dchwebb/Retrospector/Retrospector_v3/Src/initialisation.cpp

#include "stm32h743xx.h"
#include "initialisation.h"
#include "DigitalDelay.h"
#include "sdram.h"

// Clock overview:
// Main clock 4MHz: 8MHz (HSE) / 2 (M) * 200 (N) / 2 (P) = 400MHz
// SDRAM: 200MHz: Defaulted to D1 domain AHB prescaler (RCC_D1CFGR_HPRE_3) ie main clock /2 = 200MHz (AKA HCLK3)
// I2S: Peripheral Clock (AKA per_ck) set to HSI = 64MHz
// ADC: Peripheral Clock (AKA per_ck) set to HSI = 64MHz

// 8MHz (HSE) / 2 (M) * 200 (N) / 2 (P) = 400MHz
#define PLL_M1 2
#define PLL_N1 200
#define PLL_P1 1			// 0000001: pll1_p_ck = vco1_ck / 2
#define PLL_Q1 4			// This is used for I2S clock: 8MHz (HSE) / 2 (M) * 200 (N) / 4 (Q) = 200MHz
#define PLL_R1 2

void InitClocks()
{
	RCC->APB4ENR |= RCC_APB4ENR_SYSCFGEN;			// Enable System configuration controller clock

	// Voltage scaling - see Datasheet page 113. VOS1 > 300MHz; VOS2 > 200MHz; VOS3 < 200MHz
	PWR->CR3 &= ~PWR_CR3_SCUEN;						// Supply configuration update enable - this must be deactivated or VOS ready does not come on
	PWR->D3CR |= PWR_D3CR_VOS;						// Configure voltage scaling level 1 before engaging overdrive (0b11 = VOS1)
	while ((PWR->CSR1 & PWR_CSR1_ACTVOSRDY) == 0);	// Check Voltage ready 1= Ready, voltage level at or above VOS selected level

	RCC->CR |= RCC_CR_HSEON;						// Turn on external oscillator
	while ((RCC->CR & RCC_CR_HSERDY) == 0);			// Wait till HSE is ready

	// Clock source to High speed external and main (M) dividers
	RCC->PLLCKSELR = RCC_PLLCKSELR_PLLSRC_HSE |
	                 PLL_M1 << RCC_PLLCKSELR_DIVM1_Pos;

	// PLL 1 dividers
	RCC->PLL1DIVR = (PLL_N1 - 1) << RCC_PLL1DIVR_N1_Pos |
			        PLL_P1 << RCC_PLL1DIVR_P1_Pos |
			        (PLL_Q1 - 1) << RCC_PLL1DIVR_Q1_Pos |
			        (PLL_R1 - 1) << RCC_PLL1DIVR_R1_Pos;

	RCC->PLLCFGR |= RCC_PLLCFGR_PLL1RGE_2;			// 10: The PLL1 input (ref1_ck) clock range frequency is between 4 and 8 MHz (Will be 4MHz for 8MHz clock divided by 2)
	RCC->PLLCFGR &= ~RCC_PLLCFGR_PLL1VCOSEL;		// 0: Wide VCO range:192 to 836 MHz (default after reset)	1: Medium VCO range:150 to 420 MHz
	RCC->PLLCFGR |= RCC_PLLCFGR_DIVP1EN | RCC_PLLCFGR_DIVQ1EN;		// Enable divider outputs

	RCC->CR |= RCC_CR_PLL1ON;						// Turn on main PLL
	while ((RCC->CR & RCC_CR_PLL1RDY) == 0);		// Wait till PLL is ready

	// Peripheral scalers
	RCC->D1CFGR |= RCC_D1CFGR_HPRE_3;				// D1 domain AHB prescaler - divide 400MHz by 2 for 200MHz - this is then divided for all APB clocks below
	RCC->D1CFGR |= RCC_D1CFGR_D1PPRE_2; 			// Clock divider for APB3 clocks - set to 4 for 100MHz: 100: hclk / 2
	RCC->D2CFGR |= RCC_D2CFGR_D2PPRE1_2;			// Clock divider for APB1 clocks - set to 4 for 100MHz: 100: hclk / 2
	RCC->D2CFGR |= RCC_D2CFGR_D2PPRE2_2;			// Clock divider for APB2 clocks - set to 4 for 100MHz: 100: hclk / 2
	RCC->D3CFGR |= RCC_D3CFGR_D3PPRE_2;				// Clock divider for APB4 clocks - set to 4 for 100MHz: 100: hclk / 2

	RCC->CFGR |= RCC_CFGR_SW_PLL1;					// System clock switch: 011: PLL1 selected as system clock
	while ((RCC->CFGR & RCC_CFGR_SWS_Msk) != (RCC_CFGR_SW_PLL1 << RCC_CFGR_SWS_Pos));		// Wait until PLL has been selected as system clock source

	// By default Flash latency is set to 7 wait states - set to 4 for now but may need to increase
	FLASH->ACR = (FLASH->ACR & ~FLASH_ACR_LATENCY) | FLASH_ACR_LATENCY_5WS;
	while ((FLASH->ACR & FLASH_ACR_LATENCY_Msk) != FLASH_ACR_LATENCY_5WS);

	SystemCoreClockUpdate();						// Update SystemCoreClock (system clock frequency) derived from settings of oscillators, prescalers and PLL
}

GpioPin debugPinA			{GPIOB, 7, GpioPin::Type::Output};			// PB7
GpioPin debugPinB			{GPIOB, 8, GpioPin::Type::Output};			// PB8

void InitHardware()
{
	InitClocks();									// Configure the clock and PLL
	InitSysTick();

	InitADC();
	InitDAC();										// DAC used to output Wet/Dry mix levels
#ifndef NOEXTRAM
	InitSDRAM_16160();								// Initialise 32MB SDRAM
#endif
	InitCache();									// Configure MPU to not cache memory regions where DMA buffers reside
	InitLEDSPI();									// Initialise SPI/DAM for LED controller

	RCC->AHB4ENR |= RCC_AHB4ENR_GPIOBEN;			// GPIO port B clock

	// MODER: 00: Input, 01: General purpose output mode, 10: Alternate function mode, 11: Analog mode (reset state)
	// PUPDR: 00: No pull-up, pull-down, 01: Pull-up, 10: Pull-down

	// PB7 (D), PB8 (C) - I2C/debug
	GPIOB->MODER &= ~GPIO_MODER_MODE7_1;			// PB7: debug pin
	GPIOB->MODER &= ~GPIO_MODER_MODE8_1;			// PB8: debug pin

}

void InitCache()
{
	// Use the Memory Protection Unit (MPU) to set up a region of memory with data caching disabled for use with DMA buffers
	MPU->RNR = 0;									// Memory region number
	MPU->RBAR = reinterpret_cast<uint32_t>(&ADC_array);	// Store the address of the ADC_array into the region base address register

	MPU->RASR = (0b11  << MPU_RASR_AP_Pos)   |		// All access permitted
				(0b001 << MPU_RASR_TEX_Pos)  |		// Type Extension field: See truth table on p228 of Cortex M7 programming manual
				(1     << MPU_RASR_S_Pos)    |		// Shareable: provides data synchronization between bus masters. Eg a processor with a DMA controller
				(0     << MPU_RASR_C_Pos)    |		// Cacheable
				(0     << MPU_RASR_B_Pos)    |		// Bufferable (ignored for non-cacheable configuration)
				(17    << MPU_RASR_SIZE_Pos) |		// 256KB - D2 is actually 288K (size is log 2(mem size) - 1 ie 2^18 = 256k)
				(1     << MPU_RASR_ENABLE_Pos);		// Enable MPU region


	MPU->RNR = 1;									// Memory region number
	MPU->RBAR = reinterpret_cast<uint32_t>(&led); 	// Store the address of the led DMA buffer into the region base address register

	MPU->RASR = (0b11  << MPU_RASR_AP_Pos)   |		// All access permitted
				(0b001 << MPU_RASR_TEX_Pos)  |		// Type Extension field: See truth table on p228 of Cortex M7 programming manual
				(1     << MPU_RASR_S_Pos)    |		// Shareable: provides data synchronization between bus masters. Eg a processor with a DMA controller
				(0     << MPU_RASR_C_Pos)    |		// Cacheable
				(0     << MPU_RASR_B_Pos)    |		// Bufferable (ignored for non-cacheable configuration)
				(15    << MPU_RASR_SIZE_Pos) |		// 64KB - D3 (size is log 2(mem size) - 1 ie 2^16 = 64k)
				(1     << MPU_RASR_ENABLE_Pos);		// Enable MPU region



	MPU->CTRL |= (1 << MPU_CTRL_PRIVDEFENA_Pos) |	// Enable PRIVDEFENA - this allows use of default memory map for memory areas other than those specific regions defined above
				 (1 << MPU_CTRL_ENABLE_Pos);		// Enable the MPU

	// Enable data and instruction caches
	SCB_EnableDCache();
	SCB_EnableICache();
}


void InitSysTick()
{
	SysTick_Config(SystemCoreClock / SYSTICK);		// gives 1ms
	NVIC_SetPriority(SysTick_IRQn, 0);
}


void InitDAC()
{
	// DAC1_OUT2 on PA5
	RCC->AHB4ENR |= RCC_AHB4ENR_GPIOAEN;			// GPIO port clock
	RCC->APB1LENR |= RCC_APB1LENR_DAC12EN;			// Enable DAC Clock

	DAC1->CR |= DAC_CR_EN1;							// Enable DAC using PA4 (DAC_OUT1)
	DAC1->MCR &= DAC_MCR_MODE1_Msk;					// Mode = 0 means Buffer activated, Connected to external pin

	DAC1->CR |= DAC_CR_EN2;							// Enable DAC using PA5 (DAC_OUT2)
	DAC1->MCR &= DAC_MCR_MODE2_Msk;					// Mode = 0 means Buffer activated, Connected to external pin
}


void InitAdcPins(ADC_TypeDef* ADC_No, std::initializer_list<uint8_t> channels) {
	uint8_t sequence = 1;

	for (auto channel: channels) {
		// NB reset mode of GPIO pins is 0b11 = analog mode so shouldn't need to change
		ADC_No->PCSEL |= 1 << channel;					// ADC channel preselection register

		// Set conversion sequence to order ADC channels are passed to this function
		if (sequence < 5) {
			ADC_No->SQR1 |= channel << (sequence * 6);
		} else if (sequence < 10) {
			ADC_No->SQR2 |= channel << ((sequence - 5) * 6);
		} else if (sequence < 15)  {
			ADC_No->SQR3 |= channel << ((sequence - 10) * 6);
		} else {
			ADC_No->SQR4 |= channel << ((sequence - 15) * 6);
		}

		// 000: 1.5 ADC clock cycles; 001: 2.5 cycles; 010: 8.5 cycles;	011: 16.5 cycles; 100: 32.5 cycles; 101: 64.5 cycles; 110: 387.5 cycles; 111: 810.5 cycles
		if (channel < 10)
			ADC_No->SMPR1 |= 0b010 << (3 * channel);
		else
			ADC_No->SMPR2 |= 0b010 << (3 * (channel - 10));

		sequence++;
	}
}

// Settings used for both ADC1 and ADC2
void InitADC()
{
	// Configure clocks
	RCC->AHB4ENR |= RCC_AHB4ENR_GPIOAEN;			// GPIO port clock
	RCC->AHB4ENR |= RCC_AHB4ENR_GPIOBEN;
	RCC->AHB4ENR |= RCC_AHB4ENR_GPIOCEN;

	RCC->AHB1ENR |= RCC_AHB1ENR_ADC12EN;

	// 00: pll2_p_ck default, 01: pll3_r_ck clock, 10: per_ck clock*
	RCC->D3CCIPR |= RCC_D3CCIPR_ADCSEL_1;			// ADC clock selection: 10: per_ck clock (hse_ck, hsi_ker_ck or csi_ker_ck according to CKPERSEL in RCC->D1CCIPR p.353)
	RCC->AHB1ENR |= RCC_AHB1ENR_DMA1EN;

	ADC12_COMMON->CCR |= ADC_CCR_PRESC_0;			// Set prescaler to ADC clock divided by 2 (if 64MHz = 32MHz)

	InitADC1();
	InitADC2();
}


/*-----------------------------------------------------------------------------------------------------------------
ADC Channels are distributed across ADC1 and ADC2 for faster conversions. Audio channels on ADC1 for better quality.
Both insert data into ADC_array at different offsets.
 ADC1:
	0	PA3 ADC12_INP15		AUDIO_IN_L
	1	PA2 ADC12_INP14		AUDIO_IN_R
	2	PA1 ADC1_INP17		DELAY_POT_R
	3	PA0 ADC1_INP16		DELAY_CV_SCALED_R
ADC2:
	0	PC5 ADC12_INP8		WET_DRY_MIX
	1	PB1 ADC12_INP5		DELAY_POT_L
	2	PA6 ADC12_INP3 		DELAY_CV_SCALED_L
	3	PB0 ADC12_INP9		FEEDBACK_POT
	4	PA7 ADC12_INP7		FEEDBACK_CV_SCALED
	5	PC4 ADC12_INP4		FILTER_CV_SCALED
	6	PC1 ADC123_INP11 	FILTER_POT
*/

void InitADC1()
{
	// Initialize ADC peripheral
	DMA1_Stream1->CR &= ~DMA_SxCR_EN;
//	DMA1_Stream1->CR |= DMA_SxCR_CIRC;				// Circular mode to keep refilling buffer
	DMA1_Stream1->CR |= DMA_SxCR_MINC;				// Memory in increment mode
	DMA1_Stream1->CR |= DMA_SxCR_PSIZE_0;			// Peripheral size: 8 bit; 01 = 16 bit; 10 = 32 bit
	DMA1_Stream1->CR |= DMA_SxCR_MSIZE_0;			// Memory size: 8 bit; 01 = 16 bit; 10 = 32 bit
	DMA1_Stream1->CR |= DMA_SxCR_PL_0;				// Priority: 00 = low; 01 = Medium; 10 = High; 11 = Very High

	DMA1_Stream1->FCR &= ~DMA_SxFCR_FTH;			// Disable FIFO Threshold selection
	DMA1->LIFCR = 0x3F << DMA_LIFCR_CFEIF1_Pos;		// clear all five interrupts for this stream

	DMAMUX1_Channel1->CCR |= 9; 					// DMA request MUX input 9 = adc1_dma (See p.695)
	DMAMUX1_ChannelStatus->CFR |= DMAMUX_CFR_CSOF1; // Channel 1 Clear synchronization overrun event flag

	ADC1->CR &= ~ADC_CR_DEEPPWD;					// Deep powDMA1_Stream2own: 0: ADC not in deep-power down	1: ADC in deep-power-down (default reset state)
	ADC1->CR |= ADC_CR_ADVREGEN;					// Enable ADC internal voltage regulator

	// Wait until voltage regulator settled
	volatile uint32_t wait_loop_index = (SystemCoreClock / (100000UL * 2UL));
	while (wait_loop_index != 0UL) {
		wait_loop_index--;
	}
	while ((ADC1->CR & ADC_CR_ADVREGEN) != ADC_CR_ADVREGEN) {}

	ADC1->CFGR |= ADC_CFGR_CONT;					// 1: Continuous conversion mode for regular conversions
	ADC1->CFGR |= ADC_CFGR_OVRMOD;					// Overrun Mode 1: ADC_DR register is overwritten with the last conversion result when an overrun is detected.
	ADC1->CFGR |= ADC_CFGR_DMNGT_0;					// Data Management configuration 01: DMA One Shot Mode selected, 11: DMA Circular Mode selected

	// Boost mode 1: Boost mode on. Must be used when ADC clock > 20 MHz.
	ADC1->CR |= ADC_CR_BOOST_1;						// Note this sets reserved bit according to SFR - HAL has notes about silicon revision

	// For scan mode: set number of channels to be converted
	ADC1->SQR1 |= (ADC1_BUFFER_LENGTH - 1);

	// Start calibration
	ADC1->CR |= ADC_CR_ADCALLIN;					// Activate linearity calibration (as well as offset calibration)
	ADC1->CR |= ADC_CR_ADCAL;
	while ((ADC1->CR & ADC_CR_ADCAL) == ADC_CR_ADCAL) {};


	/*--------------------------------------------------------------------------------------------
	Configure ADC Channels to be converted:
	0	PA3 ADC12_INP15		AUDIO_IN_L
	1	PA2 ADC12_INP14		AUDIO_IN_R
	2	PA1 ADC1_INP17		DELAY_POT_R
	3	PA0 ADC1_INP16		DELAY_CV_SCALED_R
	*/
	InitAdcPins(ADC1, {15, 14, 17, 16});


	// Enable ADC
	ADC1->CR |= ADC_CR_ADEN;
	while ((ADC1->ISR & ADC_ISR_ADRDY) == 0) {}

	DMAMUX1_ChannelStatus->CFR |= DMAMUX_CFR_CSOF1; // Channel 1 Clear synchronization overrun event flag
	DMA1->LIFCR = 0x3F << DMA_LIFCR_CFEIF1_Pos;		// clear all five interrupts for this stream

	DMA1_Stream1->NDTR |= ADC1_BUFFER_LENGTH;		// Number of data items to transfer (ie size of ADC buffer)
	DMA1_Stream1->PAR = (uint32_t)(&(ADC1->DR));	// Configure the peripheral data register address 0x40022040
	DMA1_Stream1->M0AR = (uint32_t)(ADC_array);		// Configure the memory address (note that M1AR is used for double-buffer mode) 0x24000040

	DMA1_Stream1->CR |= DMA_SxCR_EN;				// Enable DMA and wait
	wait_loop_index = (SystemCoreClock / (100000UL * 2UL));
	while (wait_loop_index != 0UL) {
	  wait_loop_index--;
	}

	ADC1->CR |= ADC_CR_ADSTART;						// Start ADC
}



void TriggerADC1()
{
	ADC1->CR |= ADC_CR_ADSTART;
	DMA1->LIFCR |= DMA_LIFCR_CTCIF1 | DMA_LIFCR_CHTIF1;
	DMA1_Stream1->CR |= DMA_SxCR_EN;
}


void InitADC2()
{
	// Initialize ADC peripheral
	DMA1_Stream2->CR &= ~DMA_SxCR_EN;
	DMA1_Stream2->CR |= DMA_SxCR_CIRC;				// Circular mode to keep refilling buffer
	DMA1_Stream2->CR |= DMA_SxCR_MINC;				// Memory in increment mode
	DMA1_Stream2->CR |= DMA_SxCR_PSIZE_0;			// Peripheral size: 8 bit; 01 = 16 bit; 10 = 32 bit
	DMA1_Stream2->CR |= DMA_SxCR_MSIZE_0;			// Memory size: 8 bit; 01 = 16 bit; 10 = 32 bit
	DMA1_Stream2->CR |= DMA_SxCR_PL_0;				// Priority: 00 = low; 01 = Medium; 10 = High; 11 = Very High

	DMA1_Stream2->FCR &= ~DMA_SxFCR_FTH;			// Disable FIFO Threshold selection
	DMA1->LIFCR = 0x3F << DMA_LIFCR_CFEIF2_Pos;		// clear all five interrupts for this stream

	DMAMUX1_Channel2->CCR |= 10; 					// DMA request MUX input 10 = adc2_dma (See p.695)
	DMAMUX1_ChannelStatus->CFR |= DMAMUX_CFR_CSOF2; // Channel 2 Clear synchronization overrun event flag

	ADC2->CR &= ~ADC_CR_DEEPPWD;					// Deep power down: 0: ADC not in deep-power down	1: ADC in deep-power-down (default reset state)
	ADC2->CR |= ADC_CR_ADVREGEN;					// Enable ADC internal voltage regulator

	// Wait until voltage regulator settled
	volatile uint32_t wait_loop_index = (SystemCoreClock / (100000UL * 2UL));
	while (wait_loop_index != 0UL) {
		wait_loop_index--;
	}
	while ((ADC2->CR & ADC_CR_ADVREGEN) != ADC_CR_ADVREGEN) {}

	ADC2->CFGR |= ADC_CFGR_CONT;					// 1: Continuous conversion mode for regular conversions
	ADC2->CFGR |= ADC_CFGR_OVRMOD;					// Overrun Mode 1: ADC_DR register is overwritten with the last conversion result when an overrun is detected.
	ADC2->CFGR |= ADC_CFGR_DMNGT;					// Data Management configuration 11: DMA Circular Mode selected

	// Boost mode 1: Boost mode on. Must be used when ADC clock > 20 MHz.
	ADC2->CR |= ADC_CR_BOOST_1;						// Note this sets reserved bit according to SFR - HAL has notes about silicon revision
	ADC2->SQR1 |= (ADC2_BUFFER_LENGTH - 1);			// For scan mode: set number of channels to be converted

	// Start calibration
	ADC2->CR |= ADC_CR_ADCALLIN;					// Activate linearity calibration (as well as offset calibration)
	ADC2->CR |= ADC_CR_ADCAL;
	while ((ADC2->CR & ADC_CR_ADCAL) == ADC_CR_ADCAL) {};

	/* Configure ADC Channels to be converted:
	0	PC5 ADC12_INP8		WET_DRY_MIX
	1	PB1 ADC12_INP5		DELAY_POT_L
	2	PA6 ADC12_INP3 		DELAY_CV_SCALED_L
	3	PB0 ADC12_INP9		FEEDBACK_POT
	4	PA7 ADC12_INP7		FEEDBACK_CV_SCALED
	5	PC4 ADC12_INP4		FILTER_CV_SCALED
	6	PC1 ADC123_INP11 	FILTER_POT
	*/
	InitAdcPins(ADC2, {8, 5, 3, 9, 7, 4, 11});

	// Enable ADC
	ADC2->CR |= ADC_CR_ADEN;
	while ((ADC2->ISR & ADC_ISR_ADRDY) == 0) {}

	DMAMUX1_ChannelStatus->CFR |= DMAMUX_CFR_CSOF2; // Channel 2 Clear synchronization overrun event flag
	DMA1->LIFCR = 0x3F << DMA_LIFCR_CFEIF2_Pos;		// clear all five interrupts for this stream

	DMA1_Stream2->NDTR |= ADC2_BUFFER_LENGTH;		// Number of data items to transfer (ie size of ADC buffer)
	DMA1_Stream2->PAR = reinterpret_cast<uint32_t>(&(ADC2->DR));	// Configure the peripheral data register address 0x40022040
	DMA1_Stream2->M0AR = reinterpret_cast<uint32_t>(&ADC_array[ADC1_BUFFER_LENGTH]);		// Configure the memory address (note that M1AR is used for double-buffer mode) 0x24000040

	DMA1_Stream2->CR |= DMA_SxCR_EN;				// Enable DMA and wait
	wait_loop_index = (SystemCoreClock / (100000UL * 2UL));
	while (wait_loop_index != 0UL) {
		wait_loop_index--;
	}

	ADC2->CR |= ADC_CR_ADSTART;						// Start ADC
}



void InitI2S()
{
	RCC->APB1LENR |= RCC_APB1LENR_SPI2EN;			// Enable SPI clock

	GpioPin::Init(GPIOB, 9, GpioPin::Type::AlternateFunction, 5, GpioPin::DriveStrength::High);		//  PB9 I2S2_WS AF5
	GpioPin::Init(GPIOD, 3, GpioPin::Type::AlternateFunction, 5, GpioPin::DriveStrength::High);		//  PD3 I2S2_CK  AF5
	GpioPin::Init(GPIOC, 3, GpioPin::Type::AlternateFunction, 5, GpioPin::DriveStrength::High);		//  PC3 I2S2_SDO AF5

	// Configure SPI (Shown as SPI2->CGFR in SFR)
	SPI2->I2SCFGR |= SPI_I2SCFGR_I2SMOD;			// I2S Mode
	SPI2->I2SCFGR |= SPI_I2SCFGR_I2SCFG_1;			// I2S configuration mode: 00=Slave transmit; 01=Slave receive; 10=Master transmit*; 11=Master receive

	// Use a 16 bit data length but pack into the upper 16 bits of a 32 bit word
	//SPI2->I2SCFGR &= ~SPI_I2SCFGR_DATLEN;			// Data Length 00=16-bit; 01=24-bit; 10=32-bit
	SPI2->I2SCFGR |= SPI_I2SCFGR_DATLEN_1;			// Data Length 00=16-bit; 01=24-bit; *10=32-bit
	SPI2->I2SCFGR |= SPI_I2SCFGR_CHLEN;				// Channel Length = 32bits

	SPI2->CFG1 |= SPI_CFG1_UDRCFG_1;				// In the event of underrun resend last transmitted data frame
	SPI2->CFG1 |= 0x1f << SPI_CFG1_DSIZE_Pos;		// Data size to 32 bits (FIFO holds 16 bytes = 4 x 32 bit words)
	SPI2->CFG1 |= 1 << SPI_CFG1_FTHLV_Pos;			// FIFO threshold level. 0001: 2-data; 0010: 3 data; 0011: 4 data

	/* I2S Clock
		FS = I2SxCLK / [(32*2)*((2*I2SDIV)+ODD))]
		PER_CLK = 64MHz	(HSI)			64000000  / (32*2  * ((2 * 10) + 1)) = 47619.05
	*/
	RCC->D2CCIP1R |= RCC_D2CCIP1R_SPI123SEL_2;		// 000: pll1_q_ck (default); 001: pll2_p_ck; 010: pll3_p_ck; 011: I2S_CKIN; 100: per_ck
	SPI2->I2SCFGR |= (10 << SPI_I2SCFGR_I2SDIV_Pos);// Set I2SDIV to 45 with Odd factor prescaler
	SPI2->I2SCFGR |= SPI_I2SCFGR_ODD;

	SPI2->CR1 |= SPI_CR1_SPE;						// Enable I2S

	SPI2->TXDR = (int32_t)0;						// Preload the FIFO
	SPI2->TXDR = (int32_t)0;
	SPI2->TXDR = (int32_t)0;
	SPI2->TXDR = (int32_t)0;

	//SPI2->IER |= SPI_IER_TXPIE;						// Enable interrupt when TxFIFO threshold reached
	SPI2->IER |= (SPI_IER_TXPIE | SPI_IER_UDRIE);	// Enable interrupt when FIFO has free slot or underrun occurs
	NVIC_SetPriority(SPI2_IRQn, 2);					// Lower is higher priority
	NVIC_EnableIRQ(SPI2_IRQn);


	SPI2->CR1 |= SPI_CR1_CSTART;					// Start I2S
}


void suspendI2S()
{
	SPI2->CR1 |= SPI_CR1_CSUSP;
	while ((SPI2->SR & SPI_SR_SUSP) == 0);
}

void resumeI2S()
{
	extern DigitalDelay delay;
	delay.LR = left;

	// to allow resume from debugging ensure suspended then clear buffer underrun flag
	SPI2->CR1 |= SPI_CR1_CSUSP;
	while ((SPI2->SR & SPI_SR_SUSP) == 0);
	SPI2->IFCR |= SPI_IFCR_UDRC;

	// Clear suspend state and resume
	SPI2->IFCR |= SPI_IFCR_SUSPC;
	while ((SPI2->SR & SPI_SR_SUSP) != 0);
	SPI2->CR1 |= SPI_CR1_CSTART;
}

void InitDebugTimer()
{
	// Configure timer to use in internal debug timing
	RCC->APB1LENR |= RCC_APB1LENR_TIM3EN;
	TIM3->ARR = 65535;
	TIM3->PSC = 1;
	TIM3->CR1 |= TIM_CR1_CEN;
}



void InitLEDSPI()
{
	// Initialises SPI and DMA for controlling 3 RGB LEDs with Toshiba TB62781 9-way LED control (with 3k3 ohm resistors draws aroung 17mA from 5V)

	// By default clock is from APB2 peripheral clock at 100MHz (RCC_D2CFGR_D2PPRE2)
	RCC->APB4ENR |= RCC_APB4ENR_SPI6EN;

	GpioPin::Init(GPIOG, 13, GpioPin::Type::AlternateFunction, 5);		//  PG13 (128) SPI6_SCK AF5
	GpioPin::Init(GPIOG, 14, GpioPin::Type::AlternateFunction, 5);		//  PG14 (219) SPI6_MOSI  AF5

	SPI6->CR1 |= SPI_CR1_SSI;						// Internal slave select
	SPI6->CFG1 |= SPI_CFG1_MBR_2 | SPI_CFG1_MBR_0;	// Master Baud rate p2238: 100: SPI clock/32; 101: SPI clock/64
	SPI6->CFG2 |= SPI_CFG2_COMM_0;					// 00: full-duplex, *01: simplex transmitter, 10: simplex receiver, 11: half-duplex
	SPI6->CFG2 |= SPI_CFG2_SSM;						// Software slave management (ie do not use external pin)
	SPI6->CFG2 |= SPI_CFG2_SSOM;					// SS output management in master mode
	SPI6->CFG2 |= SPI_CFG2_MASTER;					// Master mode

	// Configure DMA
	RCC->AHB4ENR |= RCC_AHB4ENR_BDMAEN;

	BDMA_Channel0->CCR &= ~BDMA_CCR_MSIZE;			// Memory size: 8 bit; 01 = 16 bit; 10 = 32 bit
	BDMA_Channel0->CCR &= ~BDMA_CCR_PSIZE;			// Peripheral size: 8 bit; 01 = 16 bit; 10 = 32 bit
	BDMA_Channel0->CCR |= BDMA_CCR_DIR;				// data transfer direction: 00: peripheral-to-memory; 01: memory-to-peripheral; 10: memory-to-memory
	BDMA_Channel0->CCR |= BDMA_CCR_PL_0;			// Priority: 00 = low; 01 = Medium; 10 = High; 11 = Very High
	BDMA_Channel0->CCR |= BDMA_CCR_MINC;			// Memory in increment mode

	BDMA_Channel0->CPAR = (uint32_t)(&(SPI6->TXDR));// Configure the peripheral data register address

	DMAMUX2_Channel0->CCR |= 12; 					// DMA request MUX input 12 = spi6_tx_dma (See p.697)
	DMAMUX2_ChannelStatus->CFR |= DMAMUX_CFR_CSOF0; // Channel 5 Clear synchronization overrun event flag
}


void InitBootloaderTimer()
{
	// Timer clock operates at SysClk / 2  [specifically  ((hclk / HPRE) / D2PPRE1) * 2] = 200MHz
	RCC->APB1LENR |= RCC_APB1LENR_TIM2EN;
	TIM2->PSC = 0;									// [prescaler is PSC + 1] 200MHz / 1 = 200MHz
	TIM2->ARR = 2083;								// Set auto reload register 200MHz / 2083 = 96kHz

	TIM2->DIER |= TIM_DIER_UIE;						// DMA/interrupt enable register
	NVIC_SetPriority(TIM2_IRQn, 1);					// Lower is higher priority
	NVIC_EnableIRQ(TIM2_IRQn);

	TIM2->CR1 |= TIM_CR1_CEN;
	TIM2->EGR |= TIM_EGR_UG;						//  Re-initializes counter and generates update of registers
}


void DisableBootloaderTimer()
{
	TIM2->CR1 &= ~TIM_CR1_CEN;
	TIM2->DIER &= ~TIM_DIER_UIE;					// DMA/interrupt enable register
}


#ifdef UNUSED
// Unused
void Init_WS2812_SPI()
{
	// Initialises SPI with DMA to send data to string of WS2812B smart RGB LEDs. This uses a hacky SPI format to send serial data in NRZ format.
	// Note this requires 3x bit padding + extra dummy bytes to workaround MOSI line idling high (draws around 40mA at 5V)
	// SPI Pins:
	// PF7 (19) SPI5_SCK (only required for debugging)
	// PF9 (21) SPI5_MOSI

	// By default clock is from APB2 peripheral clock at 100MHz (RCC_D2CFGR_D2PPRE2)
	RCC->APB2ENR |= RCC_APB2ENR_SPI5EN;
	RCC->AHB4ENR |= RCC_AHB4ENR_GPIOFEN;			// GPIO port clock

	// PF7 (19) SPI5_SCK
	GPIOF->MODER  &= ~GPIO_MODER_MODE7_0;			// 10: Alternate function mode
	GPIOF->AFR[0] |= 5 << GPIO_AFRL_AFSEL7_Pos;		// Alternate Function 5 (SPI5)

	// PF9 (21) SPI5_MOSI
	GPIOF->MODER  &= ~GPIO_MODER_MODE9_0;			// 10: Alternate function mode
	GPIOF->AFR[1] |= 5 << GPIO_AFRH_AFSEL9_Pos;		// Alternate Function 5 (SPI5)

	// Configure SPI
	SPI5->CR1 |= SPI_CR1_SSI;						// Internal slave select
	SPI5->CFG1 |= SPI_CFG1_MBR_2;					// Master Baud rate p2238:  100: SPI master clock/32
	SPI5->CFG2 |= SPI_CFG2_COMM_0;					// 00: full-duplex, *01: simplex transmitter, 10: simplex receiver, 11: half-duplex
	SPI5->CFG2 |= SPI_CFG2_SSM;						// Software slave management (ie do not use external pin)
	SPI5->CFG2 |= SPI_CFG2_SSOM;					// SS output management in master mode
	SPI5->CFG2 |= SPI_CFG2_MASTER;					// Master mode
	SPI5->CFG2 |= SPI_CFG2_CPHA;					// Clock phase - this setting potentially reduces risk of MOSI line idling high (See p9 of dm00725181)

	// Configure DMA
	RCC->AHB1ENR |= RCC_AHB1ENR_DMA1EN;

	DMA1_Stream5->CR &= ~DMA_SxCR_MSIZE;			// Memory size: 8 bit; 01 = 16 bit; 10 = 32 bit
	DMA1_Stream5->CR &= ~DMA_SxCR_PSIZE;			// Peripheral size: 8 bit; 01 = 16 bit; 10 = 32 bit
	DMA1_Stream5->CR |= DMA_SxCR_DIR_0;				// data transfer direction: 00: peripheral-to-memory; 01: memory-to-peripheral; 10: memory-to-memory
	DMA1_Stream5->CR |= DMA_SxCR_PL_0;				// Priority: 00 = low; 01 = Medium; 10 = High; 11 = Very High
	DMA1_Stream5->CR |= DMA_SxCR_MINC;				// Memory in increment mode
	DMA1_Stream5->FCR &= ~DMA_SxFCR_FTH;			// FIFO threshold selection

	DMA1_Stream5->PAR = (uint32_t)(&(SPI5->TXDR));	// Configure the peripheral data register address

	DMAMUX1_Channel5->CCR |= 86; 					// DMA request MUX input 86 = spi5_tx_dma (See p.695) NB If using SPI6 need DMAMux2
	DMAMUX1_ChannelStatus->CFR |= DMAMUX_CFR_CSOF5; // Channel 5 Clear synchronization overrun event flag
}

// Unused
void InitI2C()
{
	//	Enable GPIO and I2C clocks
	RCC->APB1LENR |= RCC_APB1LENR_I2C1EN;			// I2C1 Peripheral Clocks Enable
	RCC->D2CCIP2R &= ~RCC_D2CCIP2R_I2C123SEL;		// Clock selection: 00: rcc_pclk1 (default); 01: pll3_r_ck; 10: hsi_ker_ck; 11: csi_ker_ck
	RCC->AHB4ENR |= RCC_AHB4ENR_GPIOBEN;			// GPIO port clock

	RCC->AHB1ENR |= RCC_AHB1ENR_DMA1EN;

	// Initialize I2C DMA peripheral
	DMA1_Stream0->CR &= ~DMA_SxCR_EN;
	DMA1_Stream0->CR &= ~DMA_SxCR_CIRC;				// Disable Circular mode to keep refilling buffer
	DMA1_Stream0->CR |= DMA_SxCR_MINC;				// Memory in increment mode
	DMA1_Stream0->CR &= ~DMA_SxCR_PSIZE_0;			// Peripheral size: 00 = 8 bit; 01 = 16 bit; 10 = 32 bit
	DMA1_Stream0->CR &= ~DMA_SxCR_MSIZE_0;			// Memory size: 00 = 8 bit; 01 = 16 bit; 10 = 32 bit
	DMA1_Stream0->CR |= DMA_SxCR_PL_0;				// Priority: 00 = low; 01 = Medium; 10 = High; 11 = Very High
	DMA1_Stream0->CR |= DMA_SxCR_DIR_0;				// data transfer direction: 00: peripheral-to-memory; 01: memory-to-peripheral; 10: memory-to-memory				// Priority: 00 = low; 01 = Medium; 10 = High; 11 = Very High

	DMA1_Stream0->FCR &= ~DMA_SxFCR_FTH;			// Disable FIFO Threshold selection
	DMA1->LIFCR = 0x3F << DMA_LIFCR_CFEIF0_Pos;		// clear all five interrupts for this stream

	DMAMUX1_Channel0->CCR |= 34; 					// DMA request MUX input 34 = i2c1_tx_dma (See p.695)
	DMAMUX1_ChannelStatus->CFR |= DMAMUX_CFR_CSOF0; // Channel 0 Clear synchronization overrun event flag


	// PB7: I2C1_SDA [alternate function AF4]
	GPIOB->OTYPER |= GPIO_OTYPER_OT7;				// Set pin output to Open Drain
	GPIOB->MODER &= ~GPIO_MODER_MODE7_0;			// 10: Alternate function mode
	GPIOB->AFR[0] |= 4 << GPIO_AFRL_AFSEL7_Pos;		// Alternate Function 4 (I2C1)

	// PB8: I2C1_SCL [alternate function AF4]
	GPIOB->OTYPER |= GPIO_OTYPER_OT8;				// Set pin output to Open Drain
	GPIOB->MODER &= ~GPIO_MODER_MODE8_0;			// 10: Alternate function mode
	GPIOB->AFR[1] |= 4 << GPIO_AFRH_AFSEL8_Pos;		// Alternate Function 4 (I2C1)

	//I2C1->CR1 |= I2C_CR1_ANFOFF;					// Analog noise filter - on by default
	//I2C1->CR1 |= I2C_CR1_DNF;						// Digital noise filter

	// Timings taken from HAL for 100kHz:
	// I2C1->TIMINGR =     0x10 C0 EC FF;
	// Fast mode (400kHz)  0x00 90 34 B6
	// Timing calculations: I2C frequency: 1 / ((SCLL + 1) + (SCLH + 1)) * (PRESC + 1) * 1/I2CCLK)
	// [eg 1 / ((256 + 237) * 2 * 1/100MHz) = 100kHz] (Will actually be slightly slower as there are also sync times to be accounted for)
//#define I2C_100KHZ
#ifdef I2C_100KHZ
	I2C1->TIMINGR |= 0x1 << I2C_TIMINGR_PRESC_Pos;	// Timing prescaler
	I2C1->TIMINGR |= 0x2 << I2C_TIMINGR_SDADEL_Pos;	// Data Hold Time
	I2C1->TIMINGR |= 0x4 << I2C_TIMINGR_SCLDEL_Pos;	// Data Setup Time
	I2C1->TIMINGR |= 0xFF << I2C_TIMINGR_SCLL_Pos;	// SCLL low period
	I2C1->TIMINGR |= 0xEC << I2C_TIMINGR_SCLH_Pos;	// SCLH high period
#else
	I2C1->TIMINGR |= 0x0 << I2C_TIMINGR_PRESC_Pos;	// Timing prescaler
	I2C1->TIMINGR |= 0x0 << I2C_TIMINGR_SDADEL_Pos;	// Data Hold Time
	I2C1->TIMINGR |= 0x9 << I2C_TIMINGR_SCLDEL_Pos;	// Data Setup Time
	I2C1->TIMINGR |= 0xB6 << I2C_TIMINGR_SCLL_Pos;	// SCLL low period
	I2C1->TIMINGR |= 0x34 << I2C_TIMINGR_SCLH_Pos;	// SCLH high period
#endif

	I2C1->CR1 &= ~I2C_CR1_NOSTRETCH;				// Clock stretching disable: Must be cleared in master mode
	I2C1->CR1 |= I2C_CR1_TXDMAEN;					// Enable DMA transmission

	NVIC_SetPriority(I2C1_EV_IRQn, 4);				// Lower is higher priority
	NVIC_EnableIRQ(I2C1_EV_IRQn);


	I2C1->CR1 |= I2C_CR1_PE;						// Peripheral enable
}

// Unused
void InitClockTimer()
{
	// Configure timer to use Capture and Compare mode on external clock to time duration between pulses (not using as limited in duration)

	// FIXME Production will use PA7 - temporarily using PB5 as also configured as TIM3_CH2
	// See manual page 1670 for info on Capture and Compare Input mode
	RCC->AHB4ENR |= RCC_AHB4ENR_GPIOBEN;			// GPIO port clock
	GPIOB->MODER &= ~GPIO_MODER_MODE5_0;			// Alternate function is Mode 0b10 (defaults to 0b11)
	GPIOB->AFR[0] |= 2 << GPIO_AFRL_AFSEL5_Pos;		// Alternate Function 2 for TIM3_CH2 on PB5 and PA7
	RCC->APB1LENR |= RCC_APB1LENR_TIM3EN;
	TIM3->ARR = 65535;
	TIM3->PSC = 2000;

	// TISEL Register is used to select which channel is routed to TI1, TI2, TI3 and TI4 inputs. By default CH2 is routed to TI2 so use that
	// TIM3->TISEL |= 0 << TIM_TISEL_TI2SEL_Pos;

	// There are two capture and compare registers. Configure the input to CCR1 to be CH2
	TIM3->CCMR1 |= TIM_CCMR1_CC1S_1;				// 10: CC1 channel is configured as input, IC1 is mapped on TI2

	// Configure the digital filter to allow time for the input signal to stabilise - initially set to 0
	// Note that the number of units depends on the filter clock - this is either the main timer or a subdivision set by the DTS (See CKD in CR1)
	TIM3->CCMR1 |= TIM_CCMR1_IC1F_0 & TIM_CCMR1_IC1F_1;

	// TIMx_CCER register controls detection on rising (default) or falling edge of input
	TIM3->CCER |= TIM_CCER_CC1E;					// Enable capture on 1

	// Configure the timer to reset when a rising edge is detected
	TIM3->SMCR |= 0b110 << TIM_SMCR_TS_Pos;			// 00110: Filtered Timer Input 2 (TI2FP2)
	TIM3->SMCR |= TIM_SMCR_SMS_2;					// 0100: Reset Mode - Rising edge of the selected trigger input (TRGI) reinitializes the counter

	TIM3->CR1 |= TIM_CR1_CEN;

}


void InitTempoClock()
{
	// Fire interrupt when clock pulse is received on PA7 - See manual p770
	RCC->AHB4ENR |= RCC_AHB4ENR_GPIOAEN;			// GPIO port clock
	GPIOA->MODER &= ~GPIO_MODER_MODE7_Msk;			// 00: Input mode
/*
	SYSCFG->EXTICR[1] |= SYSCFG_EXTICR2_EXTI7_PA;	// Select Pin PA7 which uses External interrupt 2
	EXTI->RTSR1 |= EXTI_RTSR1_TR7;					// Enable rising edge trigger
	EXTI->IMR1 |= EXTI_IMR1_IM7;					// Activate interrupt using mask register

	NVIC_SetPriority(EXTI9_5_IRQn, 4);				// Lower is higher priority
	NVIC_EnableIRQ(EXTI9_5_IRQn);
	*/
}
#endif

#define ITCMRAM
#ifdef ITCMRAM
void CopyToITCMRAM()
{
	/* Load functions into ITCM RAM; To use add the following GCC attribute to function:

	 void __attribute__((section(".itcm_text"))) myFunction()

	 * The following section needs to be added to the linker script:

  itcm_data = LOADADDR(.itcm_text);
  .itcm_text :
  {
    . = ALIGN(4);
    itcm_text_start = .;
    *(.itcm_text)
    *(.itcm_text*)
    . = ALIGN(4);
    itcm_text_end = .;
  } >ITCMRAM AT> FLASH


	 * */
	extern  unsigned char itcm_text_start;
	extern const unsigned char itcm_text_end;
	extern const unsigned char itcm_data;
	memcpy(&itcm_text_start, &itcm_data, (int) (&itcm_text_end - &itcm_text_start));
}
#endif


// Enter DFU bootloader - store a custom word at a known RAM address. The startup file checks for this word and jumps to bootloader in RAM if found
// STM32CubeProgrammer can be used to upload an .elf in this mode (v2.6.0 tested)
void BootDFU()
{
	SCB_DisableDCache();
	__disable_irq();
	*reinterpret_cast<unsigned long *>(0x20000000) = 0xDEADBEEF; 	// Use DTCM RAM for DFU flag as this is not cleared at restart
	__DSB();
	NVIC_SystemReset();
}
