dchwebb/Retrospector/Retrospector_v3/Src/usb/USB.h

#pragma once

#include "initialisation.h"
#include "USBHandler.h"
#include "CDCHandler.h"
#include <functional>
#include <cstring>

// Enables capturing of debug data for output over STLink UART on dev boards
#define USB_DEBUG false
#if (USB_DEBUG)
#include "uartHandler.h"
#define USB_DEBUG_COUNT 1000
#endif


// USB Hardware Registers
#define USBx_PCGCCTL	*reinterpret_cast<__IO uint32_t*>(USB2_OTG_FS_PERIPH_BASE + USB_OTG_PCGCCTL_BASE)
#define USBx_DEVICE		reinterpret_cast<USB_OTG_DeviceTypeDef*>(USB2_OTG_FS_PERIPH_BASE + USB_OTG_DEVICE_BASE)
#define USBx_INEP(i)	reinterpret_cast<USB_OTG_INEndpointTypeDef*>(USB2_OTG_FS_PERIPH_BASE + USB_OTG_IN_ENDPOINT_BASE + ((i) * USB_OTG_EP_REG_SIZE))
#define USBx_OUTEP(i)	reinterpret_cast<USB_OTG_OUTEndpointTypeDef*>(USB2_OTG_FS_PERIPH_BASE + USB_OTG_OUT_ENDPOINT_BASE + ((i) * USB_OTG_EP_REG_SIZE))
#define USBx_DFIFO(i)	*reinterpret_cast<uint32_t*>(USB2_OTG_FS_PERIPH_BASE + USB_OTG_FIFO_BASE + ((i) * USB_OTG_FIFO_SIZE))

#define EP_ADDR_MASK					0xFU
#define USB_REQ_DIRECTION_MASK			0x80U
#define USB_REQ_TYPE_MASK				0x60U

#define LOBYTE(x)  ((uint8_t)(x & 0x00FFU))
#define HIBYTE(x)  ((uint8_t)((x & 0xFF00U) >> 8U))


class USB {
	friend class USBHandler;
public:
	enum Interface {NoInterface = -1, CDCCmdInterface = 0, CDCDataInterface = 1, interfaceCount = 2};
	enum EndPoint {CDC_In = 0x81, CDC_Out = 0x1, CDC_Cmd = 0x82};
	enum EndPointType {Control = 0, Isochronous = 1, Bulk = 2, Interrupt = 3};
	enum class DeviceState {Default, Addressed, Configured, Suspended};
	enum RequestRecipient {RequestRecipientDevice = 0x0, RequestRecipientInterface = 0x1, RequestRecipientEndpoint = 0x2};
	enum RequestType {RequestTypeStandard = 0x0, RequestTypeClass = 0x20, RequestTypeVendor = 0x40};
	enum class Request {GetStatus = 0x0, SetAddress = 0x5, GetDescriptor = 0x6, SetConfiguration = 0x9};
	enum Descriptor {DeviceDescriptor = 0x1, ConfigurationDescriptor = 0x2, StringDescriptor = 0x3, InterfaceDescriptor = 0x4, EndpointDescriptor = 0x5, DeviceQualifierDescriptor = 0x6, IadDescriptor = 0xb, BosDescriptor = 0xF, ClassSpecificInterfaceDescriptor = 0x24};
	enum PacketStatus {GlobalOutNAK = 1, OutDataReceived = 2, OutTransferCompleted = 3, SetupTransComplete = 4, SetupDataReceived = 6};
	enum StringIndex {LangId = 0, Manufacturer = 1, Product = 2, Serial = 3, Configuration = 4, MassStorageClass = 5,
		CommunicationClass = 6, AudioClass = 7};

	static constexpr uint8_t ep_maxPacket = 0x40;

	void InterruptHandler();
	void Init(bool softReset);
	size_t SendData(const uint8_t *data, uint16_t len, uint8_t endpoint);
	void SendString(const char* s);
	void SendString(const std::string s);
	size_t SendString(const unsigned char* s, size_t len);
	void PauseEndpoint(USBHandler& handler);
	void ResumeEndpoint(USBHandler& handler);
	uint32_t StringToUnicode(const std::string_view desc, uint8_t* unicode);

	EP0Handler  ep0  = EP0Handler(this, 0, 0, NoInterface);
	CDCHandler  cdc  = CDCHandler(this,  USB::CDC_In,  USB::CDC_Out,  CDCCmdInterface);
	bool classPendingData = false;			// Set when class setup command received and data pending
	DeviceState devState;

private:
	enum class EP0State {Idle, Setup, DataIn, DataOut, StatusIn, StatusOut, Stall};

	static constexpr std::string_view USBD_MANUFACTURER_STRING = "Mountjoy Modular";
	static constexpr std::string_view USBD_PRODUCT_STRING = "Mountjoy Retrospector";
	static constexpr std::string_view USBD_CFG_STRING = "Mountjoy Retrospector Config";
	static constexpr std::string_view USBD_MSC_STRING = "Mountjoy Retrospector Storage";
	static constexpr std::string_view USBD_CDC_STRING = "Mountjoy Retrospector Serial";
	static constexpr std::string_view USBD_MIDI_STRING	= "Mountjoy Retrospector MIDI";
	static constexpr uint8_t usbSerialNoSize = 24;
	static constexpr uint32_t usbTimeout = 0xF000000;

	void ActivateEndpoint(uint8_t endpoint, const Direction direction, const EndPointType eptype);
	void DeactivateEndpoint(uint8_t endpoint, const Direction direction);

	void ReadPacket(const uint32_t* dest, uint16_t len, uint32_t offset);
	void WritePacket(const uint8_t* src, uint8_t endpoint, uint32_t len);
	void GetDescriptor();
	void StdDevReq();
	void EPStartXfer(const Direction direction, uint8_t endpoint, uint32_t xfer_len);
	void EP0In(const uint8_t* buff, uint32_t size);
	void CtlError();
	bool ReadInterrupts(const uint32_t interrupt);
	uint32_t MakeConfigDescriptor();
	void SerialToUnicode();

	std::array<USBHandler*, interfaceCount>classesByInterface;		// Lookup tables to get appropriate class handlers (set in handler constructor)
	std::array<USBHandler*, 2>classByEP;
	EP0State ep0State;
	bool transmitting;
	usbRequest req;

	uint8_t stringDescr[128];
	uint8_t configDescriptor[255];

	// USB standard device descriptor
	static constexpr uint16_t VendorID = 1155;	// STMicroelectronics
	static constexpr uint16_t ProductId = 65448;

	const uint8_t deviceDescr[0x12] = {
			0x12,								// bLength
			DeviceDescriptor,					// bDescriptorType
			0x01,								// bcdUSB  - 0x01 if LPM enabled
			0x02,
			0xEF,								// bDeviceClass: (Miscellaneous)
			0x02,								// bDeviceSubClass (Interface Association Descriptor- with below)
			0x01,								// bDeviceProtocol (Interface Association Descriptor)
			ep_maxPacket,  						// bMaxPacketSize
			LOBYTE(VendorID),					// idVendor
			HIBYTE(VendorID),					// idVendor
			LOBYTE(ProductId),					// idProduct
			HIBYTE(ProductId),					// idProduct
			0x00,								// bcdDevice rel. 2.00
			0x02,
			StringIndex::Manufacturer,			// Index of manufacturer  string
			StringIndex::Product,				// Index of product string
			StringIndex::Serial,				// Index of serial number string
			0x01								// bNumConfigurations
	};


	// Binary Object Store (BOS) Descriptor
	const uint8_t bosDescr[12] = {
			0x05,								// Length
			BosDescriptor,						// DescriptorType
			0x0C,								// TotalLength
			0x00, 0x01,							// NumDeviceCaps

			// USB 2.0 Extension Descriptor: device capability
			0x07,								// bLength
			0x10, 								// USB_DEVICE_CAPABITY_TYPE
			0x02,								// Attributes
			0x02, 0x00, 0x00, 0x00				// Link Power Management protocol is supported
	};


	// USB language indentifier descriptor
	static constexpr uint16_t languageIDString = 1033;
	const uint8_t langIDDescr[4] = {
			4,
			StringDescriptor,
			LOBYTE(languageIDString),
			HIBYTE(languageIDString)
	};

	const uint8_t deviceQualifierDescr[10] = {
			10,
			DeviceQualifierDescriptor,
			0x00,
			0x02,
			0x01,
			0x00,
			0x00,
			0x40,
			0x01,
			0x00,
	};


public:
#if (USB_DEBUG)
	uint16_t usbDebugNo = 0;
	uint16_t usbDebugEvent = 0;

	struct usbDebugItem {
		uint16_t eventNo;
		uint32_t Interrupt;
		uint32_t IntData;
		usbRequest Request;
		uint8_t endpoint;
		uint8_t scsiOpCode;
		uint16_t PacketSize;
		uint32_t xferBuff[4];
	};
	usbDebugItem usbDebug[USB_DEBUG_COUNT];
	void OutputDebug();

	// Update the current debug record
	void USBUpdateDbg(uint32_t IntData, usbRequest request, uint8_t endpoint, uint16_t PacketSize, uint32_t scsiOpCode, uint32_t* xferBuff)
	{
		if (usbDebugNo < USB_DEBUG_COUNT - 1) {
			if (IntData) usbDebug[usbDebugNo].IntData = IntData;
			if (((uint32_t*)&request)[0]) usbDebug[usbDebugNo].Request = request;
			if (endpoint) usbDebug[usbDebugNo].endpoint = endpoint;
			if (PacketSize) usbDebug[usbDebugNo].PacketSize = PacketSize;
			if (scsiOpCode) usbDebug[usbDebugNo].scsiOpCode = scsiOpCode;
			if (xferBuff != nullptr) {
				usbDebug[usbDebugNo].xferBuff[0] = xferBuff[0];
				usbDebug[usbDebugNo].xferBuff[1] = xferBuff[1];
				usbDebug[usbDebugNo].xferBuff[2] = xferBuff[2];
				usbDebug[usbDebugNo].xferBuff[3] = xferBuff[3];
			}
		}
	}
#else
#define USBUpdateDbg(IntData, request, endpoint, PacketSize, scsiOpCode, xferBuff)
#endif

};

extern USB usb;
