dchwebb/Retrospector/Retrospector_v3/Src/interrupts.h

void OTG_FS_IRQHandler(void) {
	usb.InterruptHandler();
}


uint32_t underrun = 0;

// I2S Interrupt
void SPI2_IRQHandler()
{
	debugPinA.SetHigh();

	if ((SPI2->SR & SPI_SR_UDR) == SPI_SR_UDR) {		// Check for Underrun condition
		SPI2->IFCR |= SPI_IFCR_UDRC;					// Clear underrun condition
		++underrun;
	}
	delay.CalcSample();

	debugPinA.SetLow();
	TriggerADC1();
}


// Audio Bootloader timer
void TIM2_IRQHandler() {
	TIM2->SR &= ~TIM_SR_UIF;				// clear Update Interrupt Flag
	//bootloader.GetSample();
	TriggerADC1();
}


// System interrupts
void NMI_Handler(void) {}

void HardFault_Handler(void) {
	while (1) {}
}
void MemManage_Handler(void) {
	while (1) {}
}
void BusFault_Handler(void) {
	while (1) {}
}
void UsageFault_Handler(void) {
	while (1) {}
}

void SVC_Handler(void) {}

void DebugMon_Handler(void) {}

void PendSV_Handler(void) {}

void SysTick_Handler(void) {
	++SysTickVal;
}

/*
// USART Decoder
void USART3_IRQHandler() {
	//if ((USART3->ISR & USART_ISR_RXNE_RXFNE) != 0 && !uartCmdRdy) {
	if (!uartCmdRdy) {
		uartCmd[uartCmdPos] = USART3->RDR; 				// accessing RDR automatically resets the receive flag
		if (uartCmd[uartCmdPos] == 10) {
			uartCmdRdy = true;
			uartCmdPos = 0;
		} else {
			uartCmdPos++;
		}
	}
}*/
